Levi-Lesches/BlueStamp-2019-Emotive-Robot/documentation/Final milestone/images/image3.jpg

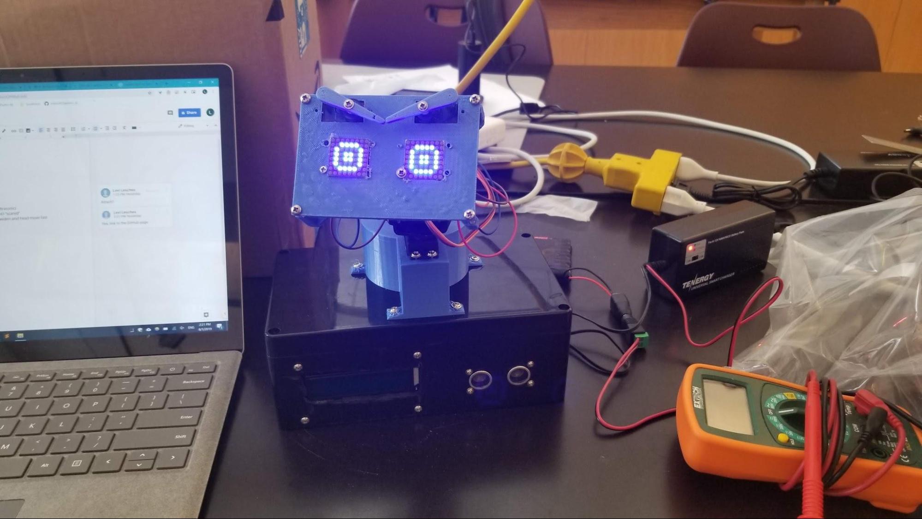
documentation/Final milestone/images/image3.jpg
