Levi-Lesches/BlueStamp-2019-Emotive-Robot/documentation/First milestone/images/image3.jpg

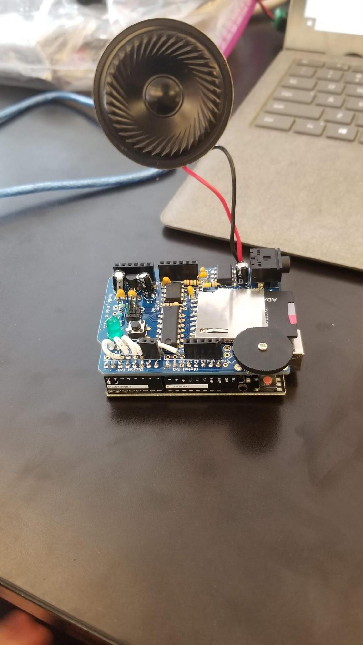
documentation/First milestone/images/image3.jpg
