Levi-Lesches/BlueStamp-2019-Emotive-Robot/documentation/Second Milestone/images/image1.jpg

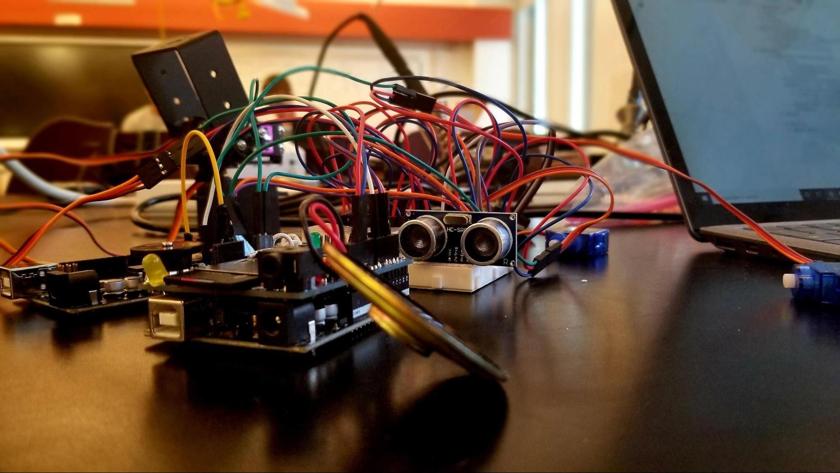
documentation/Second Milestone/images/image1.jpg
