Levi-Lesches/BlueStamp-2019-Emotive-Robot/documentation/Second Milestone/images/image3.jpg

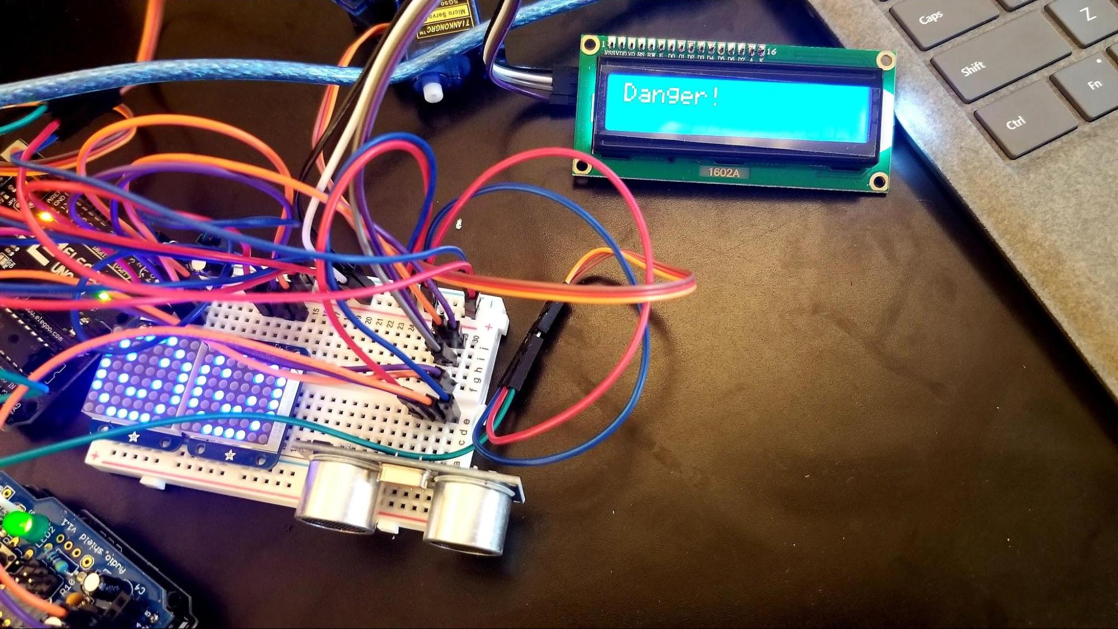
documentation/Second Milestone/images/image3.jpg
