Levi-Lesches/BlueStamp-2019-Emotive-Robot/starter/box_closing.jpg

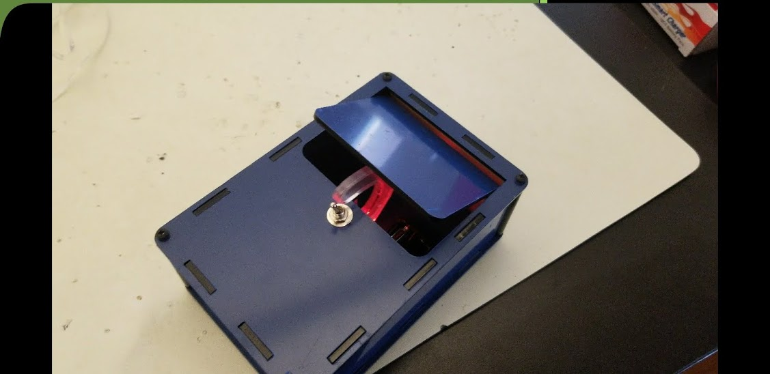
starter/box_closing.jpg
