Levi-Lesches/BlueStamp-2019-Emotive-Robot/matrix/matrix.ino

/*
	Simple sketch to blink a smiley face on the LED matrix
	Helpful for debugging problems with the LED matrix

	Pins: 
		SCL -- A5
		SDA -- A4
	
	Specs: 
		Program storage: 24%
		Dynamic memory: 24%
*/

#include <Adafruit_LEDBackpack.h>
#include <Adafruit_GFX.h>

#define SIGNAL 4

bool processing = false;
Adafruit_8x8matrix matrix = Adafruit_8x8matrix();

// https://xantorohara.github.io/led-matrix-editor/#3c4299a581a5423c
const uint8_t smile[8] = {
  B00111100,
  B01000010,
  B10100101,
  B10000001,
  B10100101,
  B10011001,
  B01000010,
  B00111100
};

void drawBitmap(uint8_t bitmap[8]) {
	matrix.drawBitmap (0, 0, bitmap, 8, 8, LED_ON);
	matrix.writeDisplay();
}

void clearMatrix() {
	matrix.clear();
	matrix.writeDisplay();
}

void setup() {
	Serial.begin (9600);
	Serial.println("Start");
	matrix.begin(0x70);
	Serial.println("End");
}

void loop() {
	drawBitmap(smile);
	delay (500);
	clearMatrix();
	delay (500);
}

// some other methods include: 
// .clear()
// .writeDisplay()
// .drawBitmap(x, y, uint8_t bitmap, width, height, LED_ON)
// .drawPixel (x, y, LED_ON/LED_OFF)
// .drawLine (x1, y1, x2, y2, LED_ON)
// .drawRect (x1, y1, x2, y2, LED_ON)
// .fillRect (x1, y1, x2, y2, LED_ON)
// .drawCircle (x, y, radius, LED_ON)
// .setTextSize (1)
// .setTextWrap (bool)
// .setTextColor(LED_ON)
// .setCursor (x, y)
// .setRotation (1-4)
